Chesstimation/Chesstimation/src/montserrat_umlaute22.cpp

/*  
    Copyright 2021, 2024, 2025 Andreas Petersik (andreas.petersik@gmail.com)
    
    This file is part of the Chesstimation Project.

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
    You should have received a copy of the GNU General Public License
    along with Chesstimation.  If not, see <https://www.gnu.org/licenses/>.
*/

/*******************************************************************************
 * Size: 22 px
 * Bpp: 4
 * Opts: --bpp 4 --size 22 --no-compress --stride 1 --align 1 --font Montserrat-Medium.ttf --symbols üó --range 32-127,161 --font FontAwesome5-Solid+Brands+Regular.woff --range 62016-62020,62087,62099,61453 --format lvgl -o montserrat_umlaute22.c
 ******************************************************************************/

#ifdef __has_include
    #if __has_include("lvgl.h")
        #ifndef LV_LVGL_H_INCLUDE_SIMPLE
            #define LV_LVGL_H_INCLUDE_SIMPLE
        #endif
    #endif
#endif

#ifdef LV_LVGL_H_INCLUDE_SIMPLE
    #include "lvgl.h"
#else
    #include "lvgl/lvgl.h"
#endif



#ifndef MONTSERRAT_UMLAUTE22
#define MONTSERRAT_UMLAUTE22 1
#endif

#if MONTSERRAT_UMLAUTE22

/*-----------------
 *    BITMAPS
 *----------------*/

/*Store the image of the glyphs*/
static LV_ATTRIBUTE_LARGE_CONST const uint8_t glyph_bitmap[] = {
    /* U+0020 " " */

    /* U+0021 "!" */
    0x4f, 0xf2, 0x3f, 0xf2, 0x3f, 0xf1, 0x2f, 0xf1,
    0x1f, 0xf0, 0x1f, 0xf0, 0xf, 0xf0, 0xf, 0xe0,
    0xf, 0xd0, 0xf, 0xd0, 0xa, 0x90, 0x0, 0x0,
    0x0, 0x0, 0x1c, 0xb1, 0x7f, 0xf5, 0x2e, 0xd1,

    /* U+0022 "\"" */
    0x9f, 0x30, 0x9f, 0x39, 0xf3, 0x9, 0xf2, 0x8f,
    0x20, 0x9f, 0x28, 0xf2, 0x8, 0xf2, 0x8f, 0x10,
    0x8f, 0x17, 0xf1, 0x8, 0xf1, 0x0, 0x0, 0x0,
    0x0,

    /* U+0023 "#" */
    0x0, 0x0, 0xf, 0x90, 0x0, 0x4f, 0x40, 0x0,
    0x0, 0x1, 0xf7, 0x0, 0x6, 0xf2, 0x0, 0x0,
    0x0, 0x3f, 0x50, 0x0, 0x8f, 0x0, 0x0, 0x0,
    0x5, 0xf3, 0x0, 0xa, 0xe0, 0x0, 0xb, 0xff,
    0xff, 0xff, 0xff, 0xff, 0xff, 0xe0, 0x7a, 0xae,
    0xfa, 0xaa, 0xaf, 0xea, 0xa9, 0x0, 0x0, 0xbd,
    0x0, 0x0, 0xf8, 0x0, 0x0, 0x0, 0xd, 0xb0,
    0x0, 0x2f, 0x60, 0x0, 0x0, 0x0, 0xf9, 0x0,
    0x4, 0xf5, 0x0, 0x0, 0x0, 0x1f, 0x70, 0x0,
    0x5f, 0x30, 0x0, 0x4a, 0xab, 0xfc, 0xaa, 0xac,
    0xfb, 0xaa, 0x16, 0xff, 0xff, 0xff, 0xff, 0xff,
    0xff, 0xf2, 0x0, 0x7, 0xf2, 0x0, 0xb, 0xd0,
    0x0, 0x0, 0x0, 0x9f, 0x0, 0x0, 0xdb, 0x0,
    0x0, 0x0, 0xa, 0xe0, 0x0, 0xf, 0x90, 0x0,
    0x0, 0x0, 0xcc, 0x0, 0x1, 0xf7, 0x0, 0x0,

    /* U+0024 "$" */
    0x0, 0x0, 0x0, 0x65, 0x0, 0x0, 0x0, 0x0,
    0x0, 0xc, 0xa0, 0x0, 0x0, 0x0, 0x0, 0x0,
    0xca, 0x0, 0x0, 0x0, 0x0, 0x3a, 0xdf, 0xfe,
    0xb6, 0x0, 0x0, 0x7f, 0xff, 0xff, 0xff, 0xfe,
    0x0, 0x3f, 0xf8, 0x1c, 0xa0, 0x4a, 0xa0, 0x9,
    0xfa, 0x0, 0xca, 0x0, 0x0, 0x0, 0xbf, 0x70,
    0xc, 0xa0, 0x0, 0x0, 0x9, 0xfc, 0x0, 0xca,
    0x0, 0x0, 0x0, 0x3f, 0xfd, 0x7c, 0xa0, 0x0,
    0x0, 0x0, 0x5e, 0xff, 0xff, 0x95, 0x0, 0x0,
    0x0, 0x6, 0xbf, 0xff, 0xfe, 0x40, 0x0, 0x0,
    0x0, 0xcc, 0x8e, 0xff, 0x30, 0x0, 0x0, 0xc,
    0xa0, 0x1c, 0xfa, 0x0, 0x0, 0x0, 0xca, 0x0,
    0x6f, 0xc0, 0x42, 0x0, 0xc, 0xa0, 0x9, 0xfa,
    0xd, 0xf9, 0x40, 0xca, 0x17, 0xff, 0x40, 0x7f,
    0xff, 0xff, 0xff, 0xff, 0x70, 0x0, 0x17, 0xbe,
    0xff, 0xda, 0x30, 0x0, 0x0, 0x0, 0xc, 0xa0,
    0x0, 0x0, 0x0, 0x0, 0x0, 0xca, 0x0, 0x0,
    0x0, 0x0, 0x0, 0x6, 0x50, 0x0, 0x0,

    /* U+0025 "%" */
    0x0, 0x7e, 0xfd, 0x40, 0x0, 0x0, 0xa, 0xf1,
    0x0, 0x7, 0xf6, 0x28, 0xf4, 0x0, 0x0, 0x4f,
    0x60, 0x0, 0xe, 0x80, 0x0, 0xbb, 0x0, 0x1,
    0xeb, 0x0, 0x0, 0x2f, 0x40, 0x0, 0x7e, 0x0,
    0x9, 0xf2, 0x0, 0x0, 0x2f, 0x40, 0x0, 0x7f,
    0x0, 0x4f, 0x60, 0x0, 0x0, 0xf, 0x80, 0x0,
    0xac, 0x0, 0xec, 0x0, 0x0, 0x0, 0x9, 0xf4,
    0x16, 0xf6, 0x9, 0xf2, 0x0, 0x0, 0x0, 0x0,
    0xaf, 0xff, 0x80, 0x3f, 0x70, 0x9f, 0xfb, 0x20,
    0x0, 0x1, 0x31, 0x0, 0xdc, 0xa, 0xe6, 0x4c,
    0xe0, 0x0, 0x0, 0x0, 0x9, 0xf2, 0x1f, 0x60,
    0x1, 0xf6, 0x0, 0x0, 0x0, 0x3f, 0x70, 0x5f,
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
    0xff, 0x80, 0x0, 0x6f, 0xff, 0xff, 0x4e, 0xff,
    0xff, 0xe0, 0x0, 0x0, 0x4e, 0xff, 0xff, 0xff,
    0xff, 0xc2, 0x0, 0x0, 0x0, 0x5, 0x9c, 0xdd,
    0xc9, 0x40, 0x0, 0x0
};


/*---------------------
 *  GLYPH DESCRIPTION
 *--------------------*/

static const lv_font_fmt_txt_glyph_dsc_t glyph_dsc[] = {
    {.bitmap_index = 0, .adv_w = 0, .box_w = 0, .box_h = 0, .ofs_x = 0, .ofs_y = 0} /* id = 0 reserved */,
    {.bitmap_index = 0, .adv_w = 95, .box_w = 0, .box_h = 0, .ofs_x = 0, .ofs_y = 0},
    {.bitmap_index = 0, .adv_w = 94, .box_w = 4, .box_h = 16, .ofs_x = 1, .ofs_y = 0},
    {.bitmap_index = 32, .adv_w = 138, .box_w = 7, .box_h = 7, .ofs_x = 1, .ofs_y = 9},
    {.bitmap_index = 57, .adv_w = 247, .box_w = 15, .box_h = 16, .ofs_x = 0, .ofs_y = 0},
    {.bitmap_index = 177, .adv_w = 219, .box_w = 13, .box_h = 22, .ofs_x = 0, .ofs_y = -3},
    {.bitmap_index = 320, .adv_w = 297, .box_w = 18, .box_h = 16, .ofs_x = 0, .ofs_y = 0},
    {.bitmap_index = 464, .adv_w = 241, .box_w = 15, .box_h = 17, .ofs_x = 0, .ofs_y = -1},
    {.bitmap_index = 592, .adv_w = 74, .box_w = 3, .box_h = 7, .ofs_x = 1, .ofs_y = 9},
    {.bitmap_index = 603, .adv_w = 119, .box_w = 5, .box_h = 21, .ofs_x = 2, .ofs_y = -4},
    {.bitmap_index = 656, .adv_w = 119, .box_w = 6, .box_h = 21, .ofs_x = 0, .ofs_y = -4},
    {.bitmap_index = 719, .adv_w = 141, .box_w = 9, .box_h = 9, .ofs_x = 0, .ofs_y = 8},
    {.bitmap_index = 760, .adv_w = 205, .box_w = 11, .box_h = 10, .ofs_x = 1, .ofs_y = 3},
    {.bitmap_index = 815, .adv_w = 80, .box_w = 3, .box_h = 7, .ofs_x = 1, .ofs_y = -3},
    {.bitmap_index = 826, .adv_w = 135, .box_w = 7, .box_h = 2, .ofs_x = 1, .ofs_y = 5},
    {.bitmap_index = 833, .adv_w = 80, .box_w = 3, .box_h = 4, .ofs_x = 1, .ofs_y = 0},
    {.bitmap_index = 839, .adv_w = 124, .box_w = 10, .box_h = 21, .ofs_x = -1, .ofs_y = -2},
    {.bitmap_index = 944, .adv_w = 235, .box_w = 13, .box_h = 16, .ofs_x = 1, .ofs_y = 0},
    {.bitmap_index = 1048, .adv_w = 130, .box_w = 6, .box_h = 16, .ofs_x = 0, .ofs_y = 0},
    {.bitmap_index = 1096, .adv_w = 202, .box_w = 12, .box_h = 16, .ofs_x = 0, .ofs_y = 0},
    {.bitmap_index = 1192, .adv_w = 201, .box_w = 12, .box_h = 16, .ofs_x = 0, .ofs_y = 0},
    {.bitmap_index = 1288, .adv_w = 235, .box_w = 15, .box_h = 16, .ofs_x = 0, .ofs_y = 0},
    {.bitmap_index = 1408, .adv_w = 202, .box_w = 12, .box_h = 16, .ofs_x = 0, .ofs_y = 0},
    {.bitmap_index = 1504, .adv_w = 217, .box_w = 12, .box_h = 16, .ofs_x = 1, .ofs_y = 0},
    {.bitmap_index = 1600, .adv_w = 210, .box_w = 13, .box_h = 16, .ofs_x = 0, .ofs_y = 0},
    {.bitmap_index = 1704, .adv_w = 227, .box_w = 14, .box_h = 16, .ofs_x = 0, .ofs_y = 0},
    {.bitmap_index = 1816, .adv_w = 217, .box_w = 13, .box_h = 16, .ofs_x = 0, .ofs_y = 0},
    {.bitmap_index = 1920, .adv_w = 80, .box_w = 3, .box_h = 12, .ofs_x = 1, .ofs_y = 0},
    {.bitmap_index = 1938, .adv_w = 80, .box_w = 3, .box_h = 15, .ofs_x = 1, .ofs_y = -3},
    {.bitmap_index = 1961, .adv_w = 205, .box_w = 11, .box_h = 11, .ofs_x = 1, .ofs_y = 2},
    {.bitmap_index = 2022, .adv_w = 205, .box_w = 11, .box_h = 7, .ofs_x = 1, .ofs_y = 4},
    {.bitmap_index = 2061, .adv_w = 205, .box_w = 11, .box_h = 11, .ofs_x = 1, .ofs_y = 2},
    {.bitmap_index = 2122, .adv_w = 202, .box_w = 12, .box_h = 16, .ofs_x = 0, .ofs_y = 0},
    {.bitmap_index = 2218, .adv_w = 364, .box_w = 21, .box_h = 20, .ofs_x = 1, .ofs_y = -4},
    {.bitmap_index = 2428, .adv_w = 258, .box_w = 18, .box_h = 16, .ofs_x = -1, .ofs_y = 0},
    {.bitmap_index = 2572, .adv_w = 266, .box_w = 14, .box_h = 16, .ofs_x = 2, .ofs_y = 0},
    {.bitmap_index = 2684, .adv_w = 251, .box_w = 15, .box_h = 16, .ofs_x = 1, .ofs_y = 0},
    {.bitmap_index = 2804, .adv_w = 291, .box_w = 16, .box_h = 16, .ofs_x = 2, .ofs_y = 0},
    {.bitmap_index = 2932, .adv_w = 236, .box_w = 12, .box_h = 16, .ofs_x = 2, .ofs_y = 0},
    {.bitmap_index = 3028, .adv_w = 224, .box_w = 12, .box_h = 16, .ofs_x = 2, .ofs_y = 0},
    {.bitmap_index = 3124, .adv_w = 272, .box_w = 15, .box_h = 16, .ofs_x = 1, .ofs_y = 0},
    {.bitmap_index = 3244, .adv_w = 286, .box_w = 14, .box_h = 16, .ofs_x = 2, .ofs_y = 0},
    {.bitmap_index = 3356, .adv_w = 109, .box_w = 3, .box_h = 16, .ofs_x = 2, .ofs_y = 0},
    {.bitmap_index = 3380, .adv_w = 181, .box_w = 11, .box_h = 16, .ofs_x = -1, .ofs_y = 0},
    {.bitmap_index = 3468, .adv_w = 253, .box_w = 14, .box_h = 16, .ofs_x = 2, .ofs_y = 0},
    {.bitmap_index = 3580, .adv_w = 209, .box_w = 11, .box_h = 16, .ofs_x = 2, .ofs_y = 0},
    {.bitmap_index = 3668, .adv_w = 336, .box_w = 17, .box_h = 16, .ofs_x = 2, .ofs_y = 0},
    {.bitmap_index = 3804, .adv_w = 286, .box_w = 14, .box_h = 16, .ofs_x = 2, .ofs_y = 0},
    {.bitmap_index = 3916, .adv_w = 296, .box_w = 17, .box_h = 16, .ofs_x = 1, .ofs_y = 0},
    {.bitmap_index = 4052, .adv_w = 254, .box_w = 13, .box_h = 16, .ofs_x = 2, .ofs_y = 0},
    {.bitmap_index = 4156, .adv_w = 296, .box_w = 18, .box_h = 19, .ofs_x = 1, .ofs_y = -3},
    {.bitmap_index = 4327, .adv_w = 256, .box_w = 13, .box_h = 16, .ofs_x = 2, .ofs_y = 0},
    {.bitmap_index = 4431, .adv_w = 219, .box_w = 13, .box_h = 16, .ofs_x = 0, .ofs_y = 0},
    {.bitmap_index = 4535, .adv_w = 207, .box_w = 13, .box_h = 16, .ofs_x = 0, .ofs_y = 0},
    {.bitmap_index = 4639, .adv_w = 278, .box_w = 14, .box_h = 16, .ofs_x = 2, .ofs_y = 0},
    {.bitmap_index = 4751, .adv_w = 251, .box_w = 17, .box_h = 16, .ofs_x = -1, .ofs_y = 0},
    {.bitmap_index = 4887, .adv_w = 396, .box_w = 25, .box_h = 16, .ofs_x = 0, .ofs_y = 0},
    {.bitmap_index = 5087, .adv_w = 237, .box_w = 15, .box_h = 16, .ofs_x = 0, .ofs_y = 0},
    {.bitmap_index = 5207, .adv_w = 228, .box_w = 16, .box_h = 16, .ofs_x = -1, .ofs_y = 0},
    {.bitmap_index = 5335, .adv_w = 231, .box_w = 14, .box_h = 16, .ofs_x = 0, .ofs_y = 0},
    {.bitmap_index = 5447, .adv_w = 117, .box_w = 5, .box_h = 21, .ofs_x = 2, .ofs_y = -4},
    {.bitmap_index = 5500, .adv_w = 124, .box_w = 10, .box_h = 21, .ofs_x = -1, .ofs_y = -2},
    {.bitmap_index = 5605, .adv_w = 117, .box_w = 6, .box_h = 21, .ofs_x = 0, .ofs_y = -4},
    {.bitmap_index = 5668, .adv_w = 205, .box_w = 11, .box_h = 10, .ofs_x = 1, .ofs_y = 3},
    {.bitmap_index = 5723, .adv_w = 176, .box_w = 11, .box_h = 3, .ofs_x = 0, .ofs_y = -2},
    {.bitmap_index = 5740, .adv_w = 211, .box_w = 7, .box_h = 3, .ofs_x = 2, .ofs_y = 14},
    {.bitmap_index = 5751, .adv_w = 210, .box_w = 11, .box_h = 12, .ofs_x = 1, .ofs_y = 0},
    {.bitmap_index = 5817, .adv_w = 240, .box_w = 13, .box_h = 17, .ofs_x = 2, .ofs_y = 0},
    {.bitmap_index = 5928, .adv_w = 201, .box_w = 12, .box_h = 12, .ofs_x = 0, .ofs_y = 0},
    {.bitmap_index = 6000, .adv_w = 240, .box_w = 13, .box_h = 17, .ofs_x = 0, .ofs_y = 0},
    {.bitmap_index = 6111, .adv_w = 215, .box_w = 13, .box_h = 12, .ofs_x = 0, .ofs_y = 0},
    {.bitmap_index = 6189, .adv_w = 124, .box_w = 9, .box_h = 17, .ofs_x = 0, .ofs_y = 0},
    {.bitmap_index = 6266, .adv_w = 243, .box_w = 14, .box_h = 16, .ofs_x = 0, .ofs_y = -4},
    {.bitmap_index = 6378, .adv_w = 240, .box_w = 12, .box_h = 17, .ofs_x = 2, .ofs_y = 0},
    {.bitmap_index = 6480, .adv_w = 98, .box_w = 4, .box_h = 17, .ofs_x = 1, .ofs_y = 0},
    {.bitmap_index = 6514, .adv_w = 100, .box_w = 8, .box_h = 21, .ofs_x = -3, .ofs_y = -4},
    {.bitmap_index = 6598, .adv_w = 216, .box_w = 12, .box_h = 17, .ofs_x = 2, .ofs_y = 0},
    {.bitmap_index = 6700, .adv_w = 98, .box_w = 3, .box_h = 17, .ofs_x = 2, .ofs_y = 0},
    {.bitmap_index = 6726, .adv_w = 372, .box_w = 20, .box_h = 12, .ofs_x = 2, .ofs_y = 0},
    {.bitmap_index = 6846, .adv_w = 240, .box_w = 12, .box_h = 12, .ofs_x = 2, .ofs_y = 0},
    {.bitmap_index = 6918, .adv_w = 224, .box_w = 14, .box_h = 12, .ofs_x = 0, .ofs_y = 0},
    {.bitmap_index = 7002, .adv_w = 240, .box_w = 13, .box_h = 16, .ofs_x = 2, .ofs_y = -4},
    {.bitmap_index = 7106, .adv_w = 240, .box_w = 13, .box_h = 16, .ofs_x = 0, .ofs_y = -4},
    {.bitmap_index = 7210, .adv_w = 144, .box_w = 7, .box_h = 12, .ofs_x = 2, .ofs_y = 0},
    {.bitmap_index = 7252, .adv_w = 176, .box_w = 11, .box_h = 12, .ofs_x = 0, .ofs_y = 0},
    {.bitmap_index = 7318, .adv_w = 146, .box_w = 9, .box_h = 15, .ofs_x = 0, .ofs_y = 0},
    {.bitmap_index = 7386, .adv_w = 238, .box_w = 12, .box_h = 12, .ofs_x = 1, .ofs_y = 0},
    {.bitmap_index = 7458, .adv_w = 197, .box_w = 14, .box_h = 12, .ofs_x = -1, .ofs_y = 0},
    {.bitmap_index = 7542, .adv_w = 316, .box_w = 20, .box_h = 12, .ofs_x = 0, .ofs_y = 0},
    {.bitmap_index = 7662, .adv_w = 194, .box_w = 12, .box_h = 12, .ofs_x = 0, .ofs_y = 0},
    {.bitmap_index = 7734, .adv_w = 197, .box_w = 14, .box_h = 16, .ofs_x = -1, .ofs_y = -4},
    {.bitmap_index = 7846, .adv_w = 183, .box_w = 11, .box_h = 12, .ofs_x = 0, .ofs_y = 0},
    {.bitmap_index = 7912, .adv_w = 124, .box_w = 7, .box_h = 21, .ofs_x = 1, .ofs_y = -4},
    {.bitmap_index = 7986, .adv_w = 105, .box_w = 3, .box_h = 21, .ofs_x = 2, .ofs_y = -4},
    {.bitmap_index = 8018, .adv_w = 124, .box_w = 7, .box_h = 21, .ofs_x = 0, .ofs_y = -4},
    {.bitmap_index = 8092, .adv_w = 205, .box_w = 11, .box_h = 4, .ofs_x = 1, .ofs_y = 6},
    {.bitmap_index = 8114, .adv_w = 94, .box_w = 4, .box_h = 16, .ofs_x = 1, .ofs_y = -4},
    {.bitmap_index = 8146, .adv_w = 224, .box_w = 14, .box_h = 17, .ofs_x = 0, .ofs_y = 0},
    {.bitmap_index = 8265, .adv_w = 238, .box_w = 12, .box_h = 17, .ofs_x = 1, .ofs_y = 0},
    {.bitmap_index = 8367, .adv_w = 242, .box_w = 16, .box_h = 16, .ofs_x = 0, .ofs_y = 0},
    {.bitmap_index = 8495, .adv_w = 440, .box_w = 28, .box_h = 15, .ofs_x = 0, .ofs_y = 1},
    {.bitmap_index = 8705, .adv_w = 440, .box_w = 28, .box_h = 15, .ofs_x = 0, .ofs_y = 1},
    {.bitmap_index = 8915, .adv_w = 440, .box_w = 28, .box_h = 15, .ofs_x = 0, .ofs_y = 1},
    {.bitmap_index = 9125, .adv_w = 440, .box_w = 28, .box_h = 15, .ofs_x = 0, .ofs_y = 1},
    {.bitmap_index = 9335, .adv_w = 440, .box_w = 28, .box_h = 15, .ofs_x = 0, .ofs_y = 1},
    {.bitmap_index = 9545, .adv_w = 440, .box_w = 28, .box_h = 18, .ofs_x = 0, .ofs_y = -1},
    {.bitmap_index = 9797, .adv_w = 308, .box_w = 17, .box_h = 23, .ofs_x = 1, .ofs_y = -3}
};

/*---------------------
 *  CHARACTER MAPPING
 *--------------------*/

static const uint16_t unicode_list_1[] = {
    0x0, 0x52, 0x5b, 0xef6c, 0xf19f, 0xf1a0, 0xf1a1, 0xf1a2,
    0xf1a3, 0xf1e6, 0xf1f2
};

/*Collect the unicode lists and glyph_id offsets*/
static const lv_font_fmt_txt_cmap_t cmaps[] =
{
    {
        .range_start = 32, .range_length = 95, .glyph_id_start = 1,
        .unicode_list = NULL, .glyph_id_ofs_list = NULL, .list_length = 0, .type = LV_FONT_FMT_TXT_CMAP_FORMAT0_TINY
    },
    {
        .range_start = 161, .range_length = 61939, .glyph_id_start = 96,
        .unicode_list = unicode_list_1, .glyph_id_ofs_list = NULL, .list_length = 11, .type = LV_FONT_FMT_TXT_CMAP_SPARSE_TINY
    }
};



/*--------------------
 *  ALL CUSTOM DATA
 *--------------------*/

#if LVGL_VERSION_MAJOR == 8
/*Store all the custom data of the font*/
static  lv_font_fmt_txt_glyph_cache_t cache;
#endif

#if LVGL_VERSION_MAJOR >= 8
static const lv_font_fmt_txt_dsc_t font_dsc = {
#else
static lv_font_fmt_txt_dsc_t font_dsc = {
#endif
    .glyph_bitmap = glyph_bitmap,
    .glyph_dsc = glyph_dsc,
    .cmaps = cmaps,
    .kern_dsc = NULL,
    .kern_scale = 0,
    .cmap_num = 2,
    .bpp = 4,
    .kern_classes = 0,
    .bitmap_format = 0,
#if LVGL_VERSION_MAJOR == 8
    .cache = &cache
#endif

};

extern const lv_font_t lv_font_montserrat_22;


/*-----------------
 *  PUBLIC FONT
 *----------------*/

/*Initialize a public general font descriptor*/
#if LVGL_VERSION_MAJOR >= 8
lv_font_t montserrat_umlaute22 = {
#else
lv_font_t montserrat_umlaute22 = {
#endif
    .get_glyph_dsc = lv_font_get_glyph_dsc_fmt_txt,    /*Function pointer to get glyph's data*/
    .get_glyph_bitmap = lv_font_get_bitmap_fmt_txt,    /*Function pointer to get glyph's bitmap*/
    .line_height = 24,          /*The maximum line height required by the font*/
    .base_line = 4,             /*Baseline measured from the bottom of the line*/
#if !(LVGL_VERSION_MAJOR == 6 && LVGL_VERSION_MINOR == 0)
    .subpx = LV_FONT_SUBPX_NONE,
#endif
    .static_bitmap = 0,
#if LV_VERSION_CHECK(7, 4, 0) || LVGL_VERSION_MAJOR >= 8
    .underline_position = -2,
    .underline_thickness = 1,
#endif
    .dsc = &font_dsc,          /*The custom font data. Will be accessed by `get_glyph_bitmap/dsc` */
#if LV_VERSION_CHECK(8, 2, 0) || LVGL_VERSION_MAJOR >= 9
    .fallback = &lv_font_montserrat_22,
#endif
    .user_data = NULL,
};



#endif /*#if MONTSERRAT_UMLAUTE22*/
