Chesstimation/Chesstimation/src/pieces-bitmaps.cpp

/*  
    Copyright 2021, 2024 Andreas Petersik (andreas.petersik@gmail.com)
    
    This file is part of the Chesstimation Project.

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
    You should have received a copy of the GNU General Public License
    along with Chesstimation.  If not, see <https://www.gnu.org/licenses/>.
*/

#ifdef __has_include
    #if __has_include("lvgl.h")
        #ifndef LV_CONF_INCLUDE_SIMPLE
            #define LV_CONF_INCLUDE_SIMPLE
        #endif
    #endif
#endif

#if defined(LV_CONF_INCLUDE_SIMPLE)
    #include "lvgl.h"
#else
    #include "lvgl/lvgl.h"
#endif


#ifndef LV_ATTRIBUTE_MEM_ALIGN
#define LV_ATTRIBUTE_MEM_ALIGN
#endif

#ifndef LV_ATTRIBUTE_IMAGE_BB40
#define LV_ATTRIBUTE_IMAGE_BB40
#endif

const LV_ATTRIBUTE_MEM_ALIGN LV_ATTRIBUTE_LARGE_CONST LV_ATTRIBUTE_IMAGE_BB40 uint8_t BB40_map[] = {
  0x00, 0x00, 0x00, 0x00, 0x00, 0x00, 0x00, 0x00, 0x00, 0x00, 0x00, 0x00, 0x00, 0x00, 0x00, 0x00, 0x00, 0x00, 0x00, 0x00, 0x00, 0x00, 0x00, 0x00, 0x00, 0x00, 0x00, 0x00, 0x00, 0x00, 0x00, 0x00, 0x00, 0x00, 0x00, 0x00, 0x00, 0x00, 0x00, 0x00, 0x00, 0x00, 0x00, 0x00, 0x00, 0x00, 0x00, 0x00, 0x00, 0x00, 0x00, 0x00, 0x00, 0x00, 0x00, 0x00, 0x00, 0x00, 0x00, 0x00, 0x00, 0x00, 0x00, 0x00, 0x00, 0x00, 0x00, 0x00, 0x00, 0x00, 0x00, 0x00, 0x00, 0x00, 0x00, 0x00, 0x00, 0x00, 0x00, 0x00, 
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
};

lv_image_dsc_t BP40 = {
  {
  .magic = LV_IMAGE_HEADER_MAGIC,
  .cf = LV_COLOR_FORMAT_RGB565A8,
  .w = 40,
  .h = 40,
  },
  .data_size = 1600 * 3,
  .data = BP40_map,
};

#ifndef LV_ATTRIBUTE_IMAGE_BQ40
#define LV_ATTRIBUTE_IMAGE_BQ40
#endif
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
